HORIZOP-Energy/horizop-ECSACP1-PCB-design/Resources/ESP_WROVER_KIT/ESP-WROVER-KIT_V3_Protective_Case/Wrover-Kit-V3-Top.stl

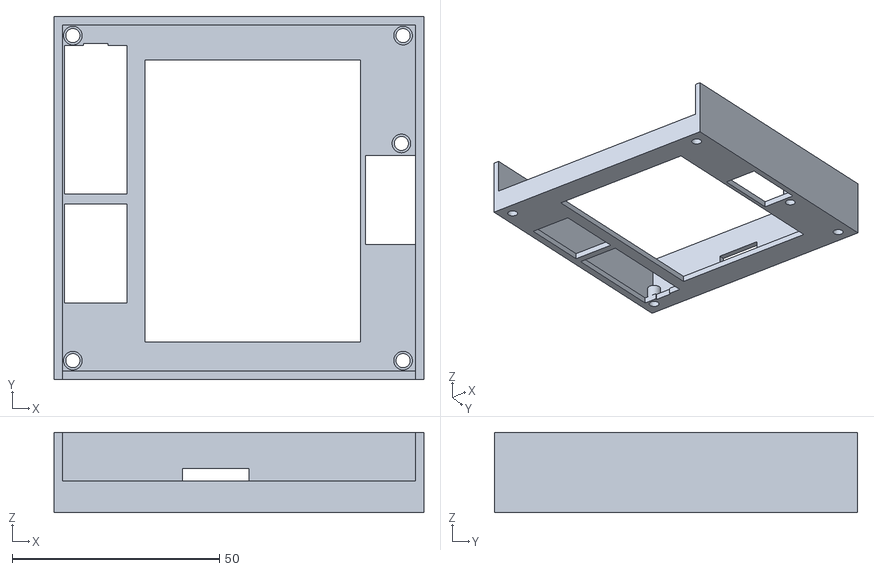
[picture p13: CAD file, 2023-11-17]
Resources/ESP_WROVER_KIT/ESP-WROVER-KIT_V3_Protective_Case/Wrover-Kit-V3-Top.stl
89.1 x 87.5 x 19.3
