HORIZOP-Energy/horizop-ECSACP1-PCB-design/Resources/ESP_WROVER_KIT/ESP32-WROVER-E/ESP32-WROVER-B&IB&E&IE PCB Footprint.dxf

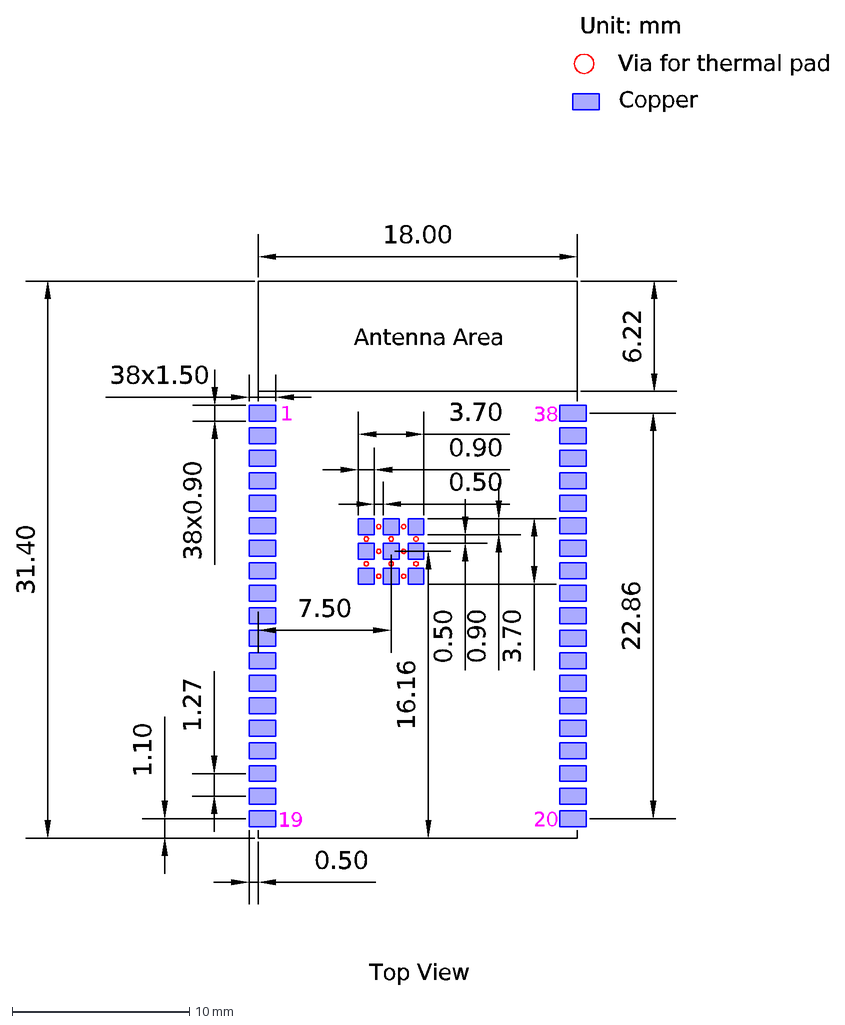
[picture p14: CAD file, 2023-11-17]
Resources/ESP_WROVER_KIT/ESP32-WROVER-E/ESP32-WROVER-B&IB&E&IE PCB Footprint.dxf
Unit: mm
Copper
Via for thermal pad
Antenna Area
Top View
1
19
20
38
38x1.50
38x0.90
18.00
31.40
1.27
1.10
6.22
0.50
22.86
3.70
0.90
16.16
7.50
