HORIZOP-Energy/horizop-ECSACP1-PCB-design/Resources/HLK-5M05/HLK-5M05.step

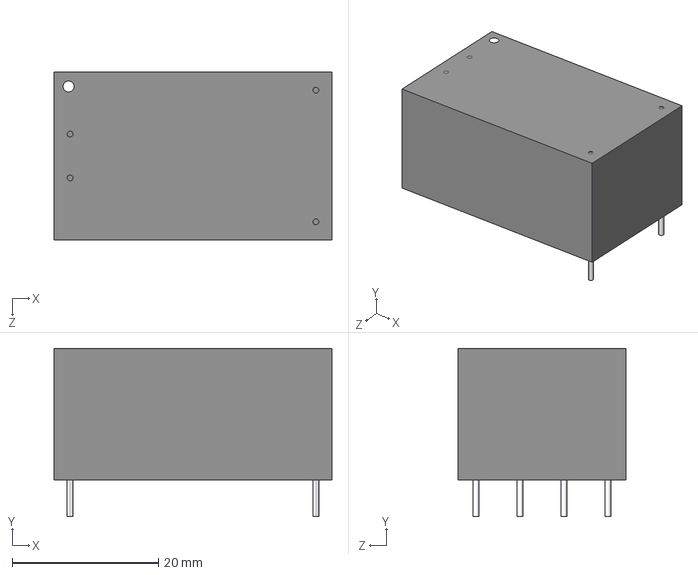
[picture p15: CAD file, 2023-11-17]
Resources/HLK-5M05/HLK-5M05.step
38.0 x 23.0 x 23.0 mm
