HORIZOP-Energy/horizop-ECSACP1-PCB-design/Resources/MCP602-I_P/MCP602-I_P.step

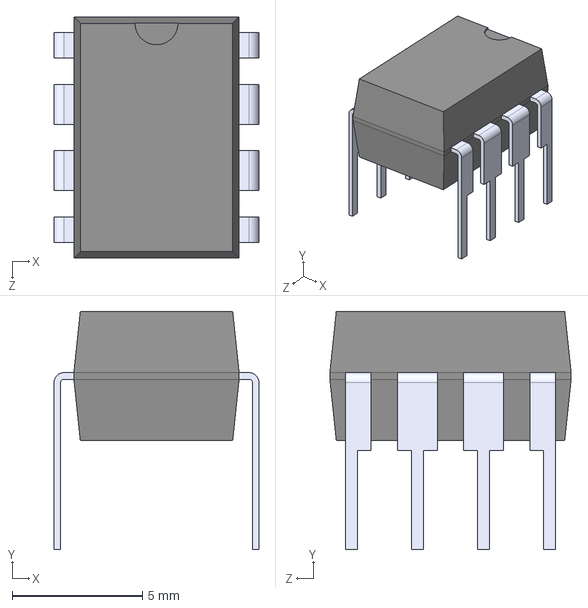
[picture p16: CAD file, 2023-11-17]
Resources/MCP602-I_P/MCP602-I_P.step
7.87 x 9.14 x 9.27 mm
