HORIZOP-Energy/horizop-ECSACP1-PCB-design/Resources/ESP_WROVER_KIT/ESP-WROVER-KIT_V3_Protective_Case/Wrover-Kit-V3-Bot.stl

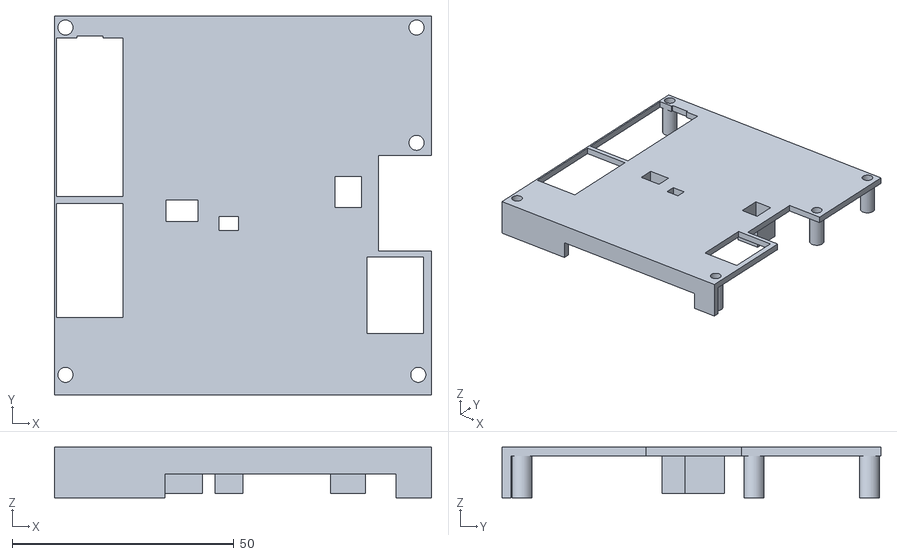
[picture p17: CAD file, 2023-11-17]
Resources/ESP_WROVER_KIT/ESP-WROVER-KIT_V3_Protective_Case/Wrover-Kit-V3-Bot.stl
85.1 x 85.5 x 11.5
