HORIZOP-Energy/horizop-ECSACP1-PCB-design/SOLIDWORKS_Files/HE_ECSACP1_PCB_V9_Final/mps_dcdc_nma_dc_a_HE_ECSACP1_PCB_V9.sldprt

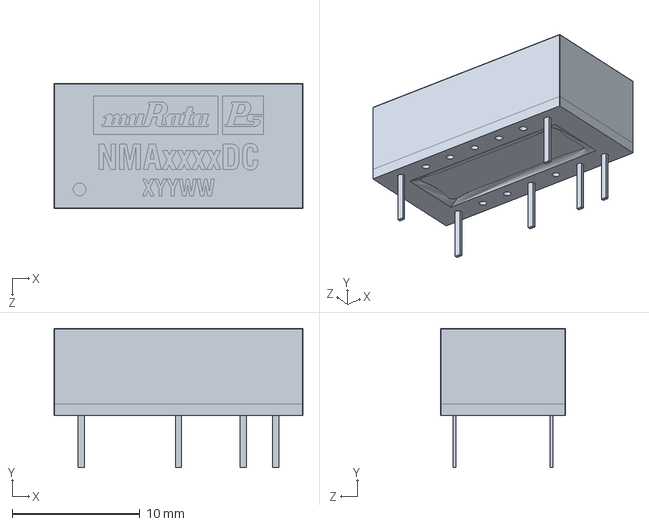
[picture p18: CAD file, 2023-11-17]
SOLIDWORKS_Files/HE_ECSACP1_PCB_V9_Final/mps_dcdc_nma_dc_a_HE_ECSACP1_PCB_V9.sldprt
19.5 x 10.9 x 9.80 mm
