HORIZOP-Energy/horizop-ECSACP1-PCB-design/SOLIDWORKS_Files/HE_ECSACP1_PCB_V9_Final/vb 0,5-1-12_HE_ECSACP1_PCB_V9.SLDPRT

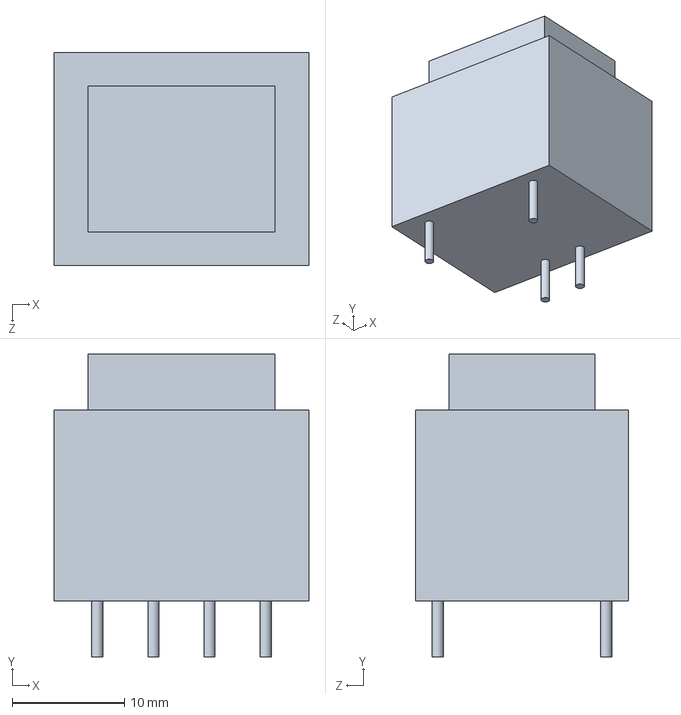
[picture p19: CAD file, 2023-11-17]
SOLIDWORKS_Files/HE_ECSACP1_PCB_V9_Final/vb 0,5-1-12_HE_ECSACP1_PCB_V9.SLDPRT
22.7 x 27.0 x 19.0 mm
