HORIZOP-Energy/horizop-ECSACP1-PCB-design/SOLIDWORKS_Files/HE_ECSACP1_PCB_V9_With_ESP_WROVER_KIT_V4.1_Final/User Library-TAKAMISAWA RY12W-K.sldprt

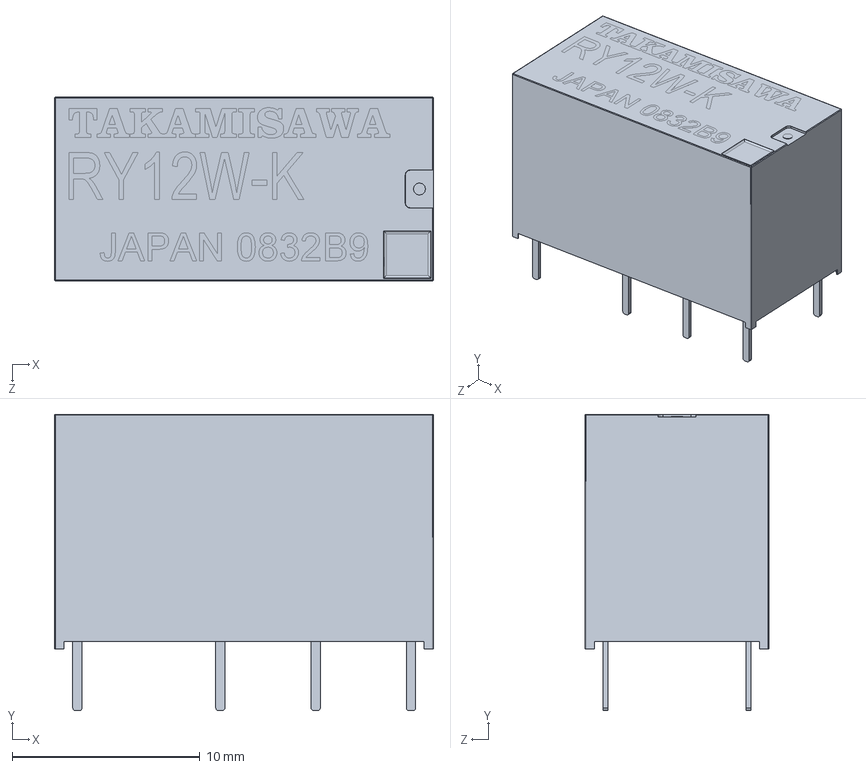
[picture p20: CAD file, 2023-11-17]
SOLIDWORKS_Files/HE_ECSACP1_PCB_V9_With_ESP_WROVER_KIT_V4.1_Final/User Library-TAKAMISAWA RY12W-K.sldprt
20.2 x 15.8 x 9.80 mm
