HORIZOP-Energy/horizop-ECSACP1-PCB-design/SOLIDWORKS_Files/HE_ECSACP1_PCB_V9_With_ESP_WROVER_KIT_V4.1_Final/ESP-WROVER_KIT_V4.1_HE_ECSACP1_PCB_V9.SLDPRT

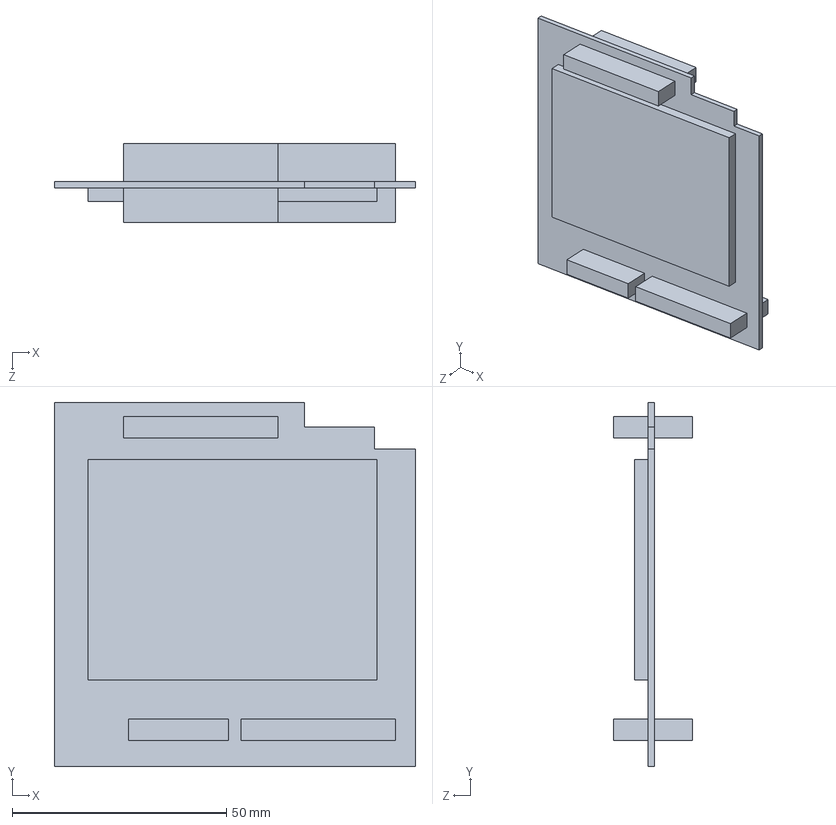
[picture p21: CAD file, 2023-11-17]
SOLIDWORKS_Files/HE_ECSACP1_PCB_V9_With_ESP_WROVER_KIT_V4.1_Final/ESP-WROVER_KIT_V4.1_HE_ECSACP1_PCB_V9.SLDPRT
84.3 x 85.1 x 18.4 mm
