HORIZOP-Energy/horizop-ECSACP1-PCB-design/SOLIDWORKS_Files/HE_ECSACP1_PCB_V9_Final/DG142R-6-5.08_HE_ECSACP1_PCB_V9.SLDPRT

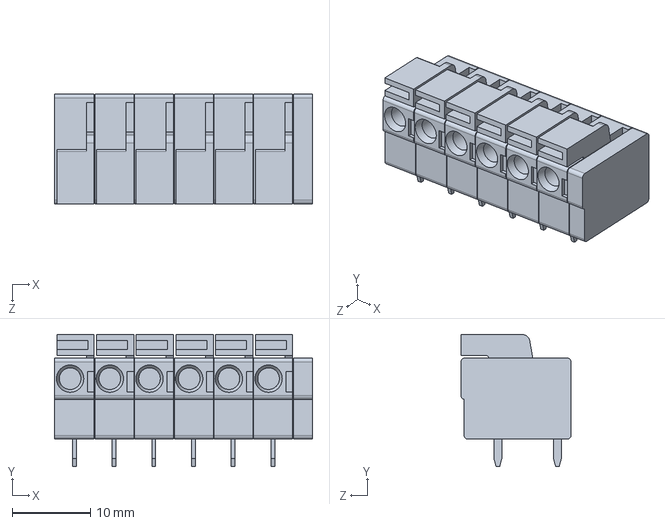
[picture p22: CAD file, 2023-11-17]
SOLIDWORKS_Files/HE_ECSACP1_PCB_V9_Final/DG142R-6-5.08_HE_ECSACP1_PCB_V9.SLDPRT
33.0 x 16.9 x 14.1 mm
