HORIZOP-Energy/horizop-ECSACP1-PCB-design/SOLIDWORKS_Files/HE_ECSACP1_PCB_V9_Final/DG142R-2-5.08_HE_ECSACP1_PCB_V9.SLDPRT

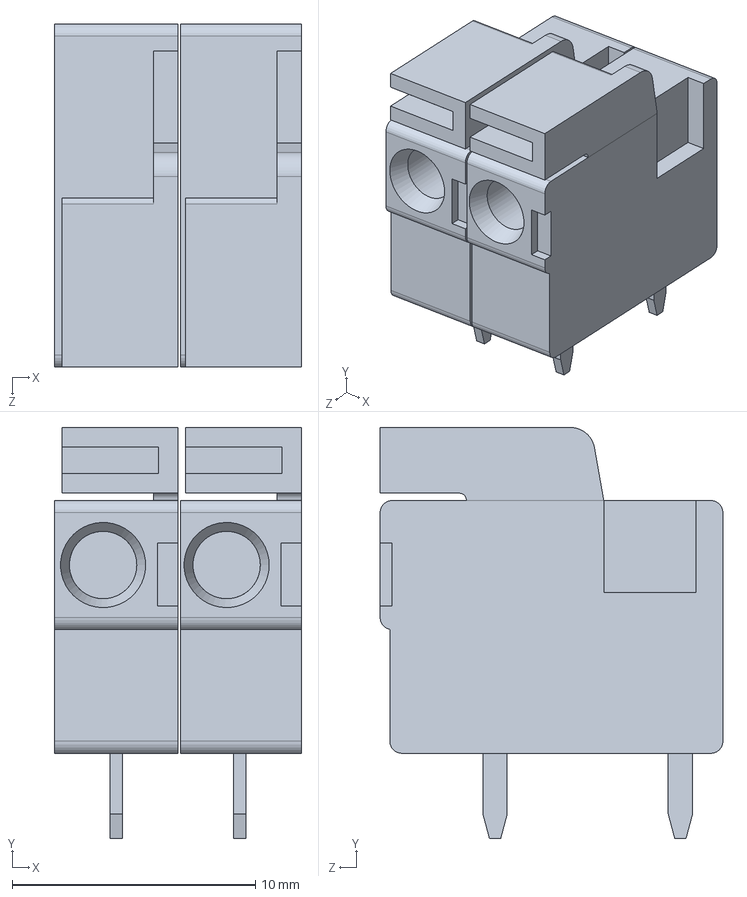
[picture p23: CAD file, 2023-11-17]
SOLIDWORKS_Files/HE_ECSACP1_PCB_V9_Final/DG142R-2-5.08_HE_ECSACP1_PCB_V9.SLDPRT
10.2 x 16.9 x 14.1 mm
