HORIZOP-Energy/horizop-ECSACP1-PCB-design/SOLIDWORKS_Files/HE_ECSACP1_PCB_V9_Final/sj1-3513n_HE_ECSACP1_PCB_V9.SLDPRT

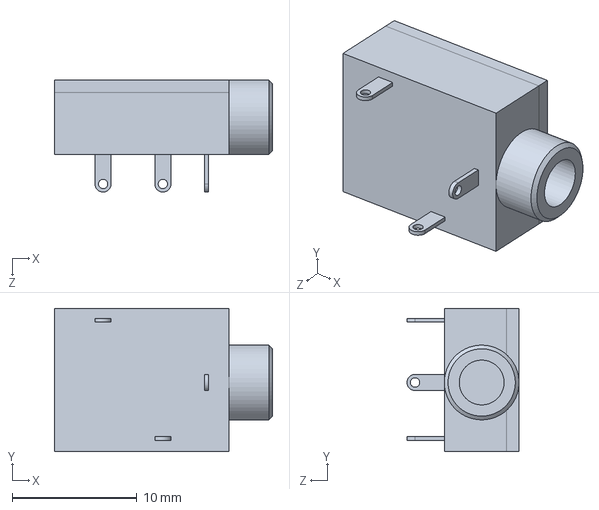
[picture p24: CAD file, 2023-11-17]
SOLIDWORKS_Files/HE_ECSACP1_PCB_V9_Final/sj1-3513n_HE_ECSACP1_PCB_V9.SLDPRT
17.5 x 11.5 x 9.00 mm
