HORIZOP-Energy/horizop-ECSACP1-PCB-design/Resources/Printer_settings.png

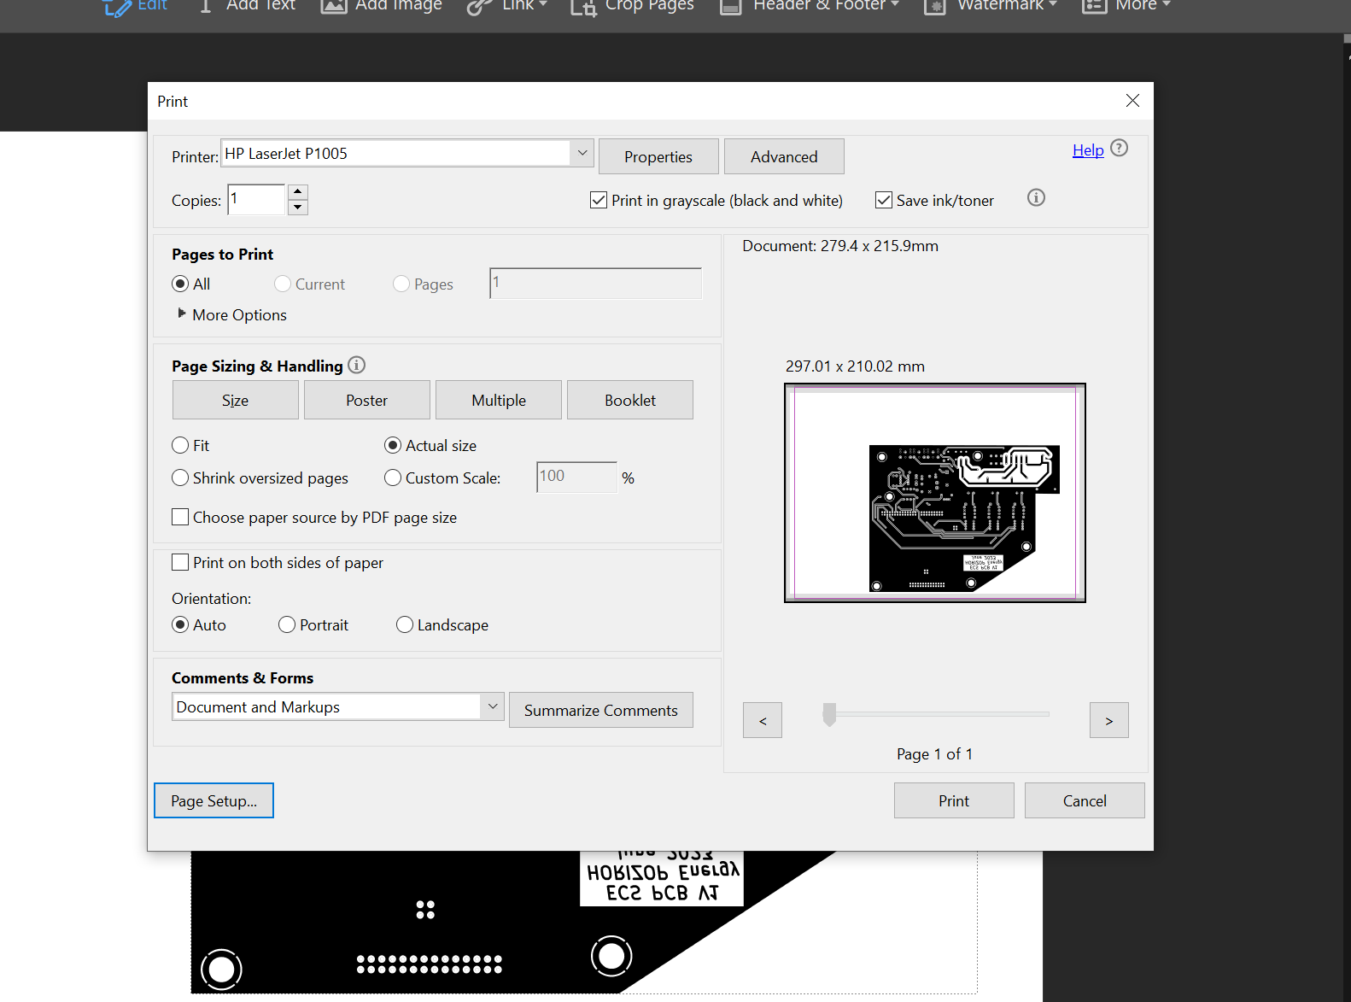
Resources/Printer_settings.png
